manuver-se/Deimos-4/documentation/schematics/midimod/IMG_1283.jpeg

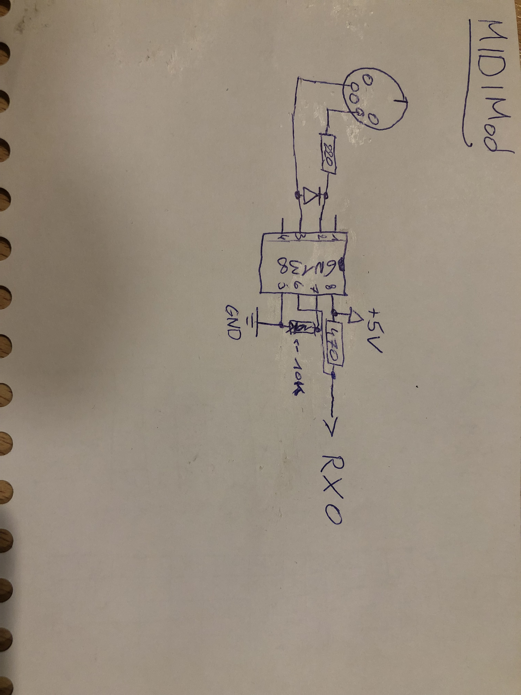
documentation/schematics/midimod/IMG_1283.jpeg
